romangrdlv/antenna-2415/images/calc.jpg

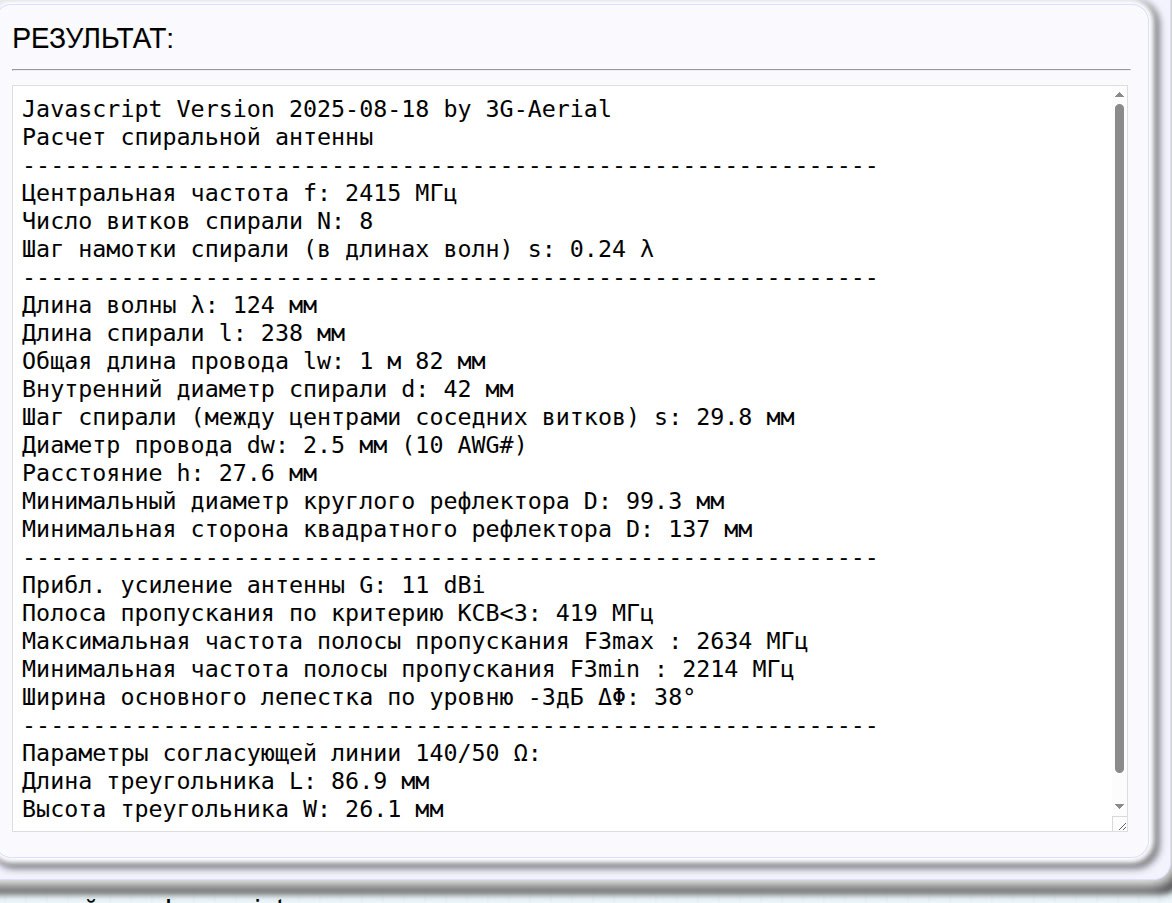
images/calc.jpg
