romangrdlv/antenna-2415/images/isolation.jpg

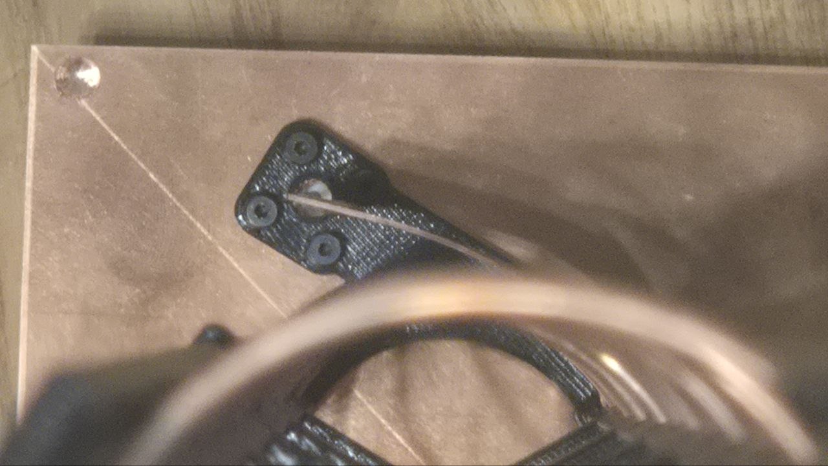
images/isolation.jpg
