romangrdlv/antenna-2415/images/reflector_back.jpg

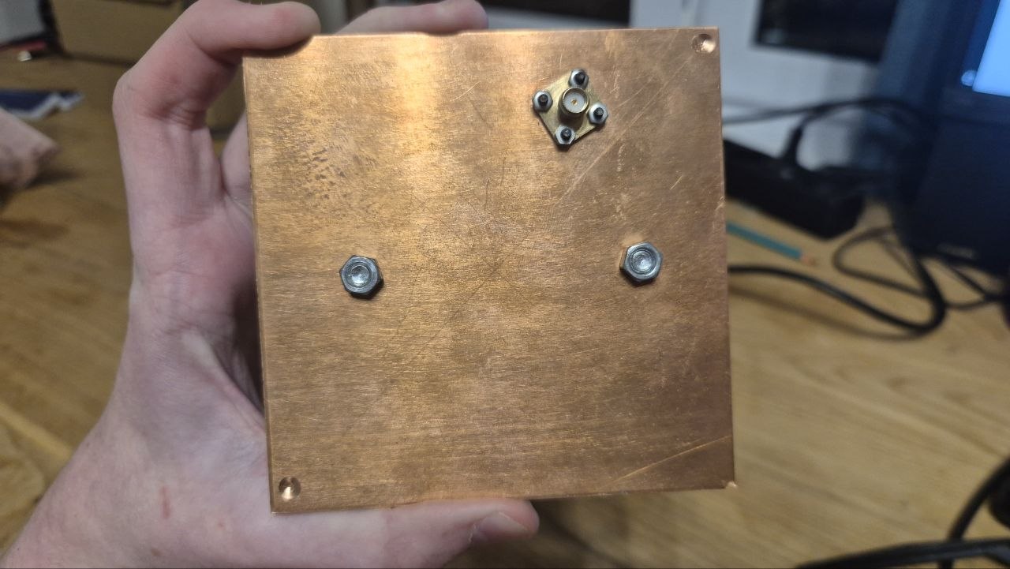
images/reflector_back.jpg
