romangrdlv/antenna-2415/images/test.jpg

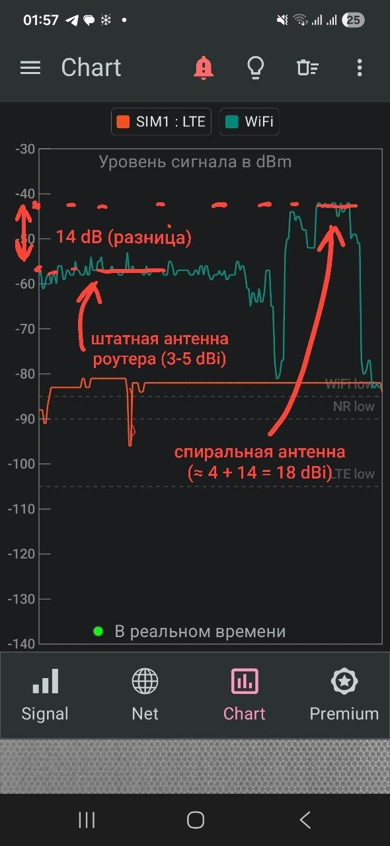
images/test.jpg
